WillyCcV19/PI_Equipo_04/ProyectoIntegrador/Entegables/P-CajaFuncionesYEsquemaFunciones.md

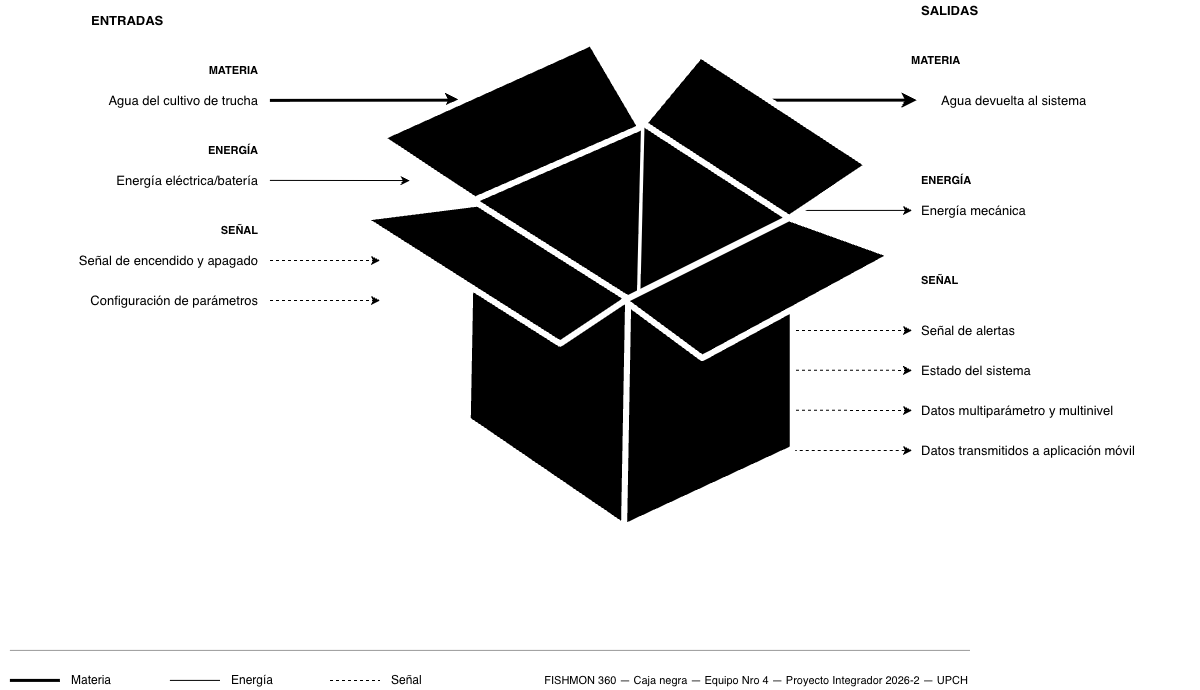
[picture p103: Imagenes/func/cajanegra-final.png]

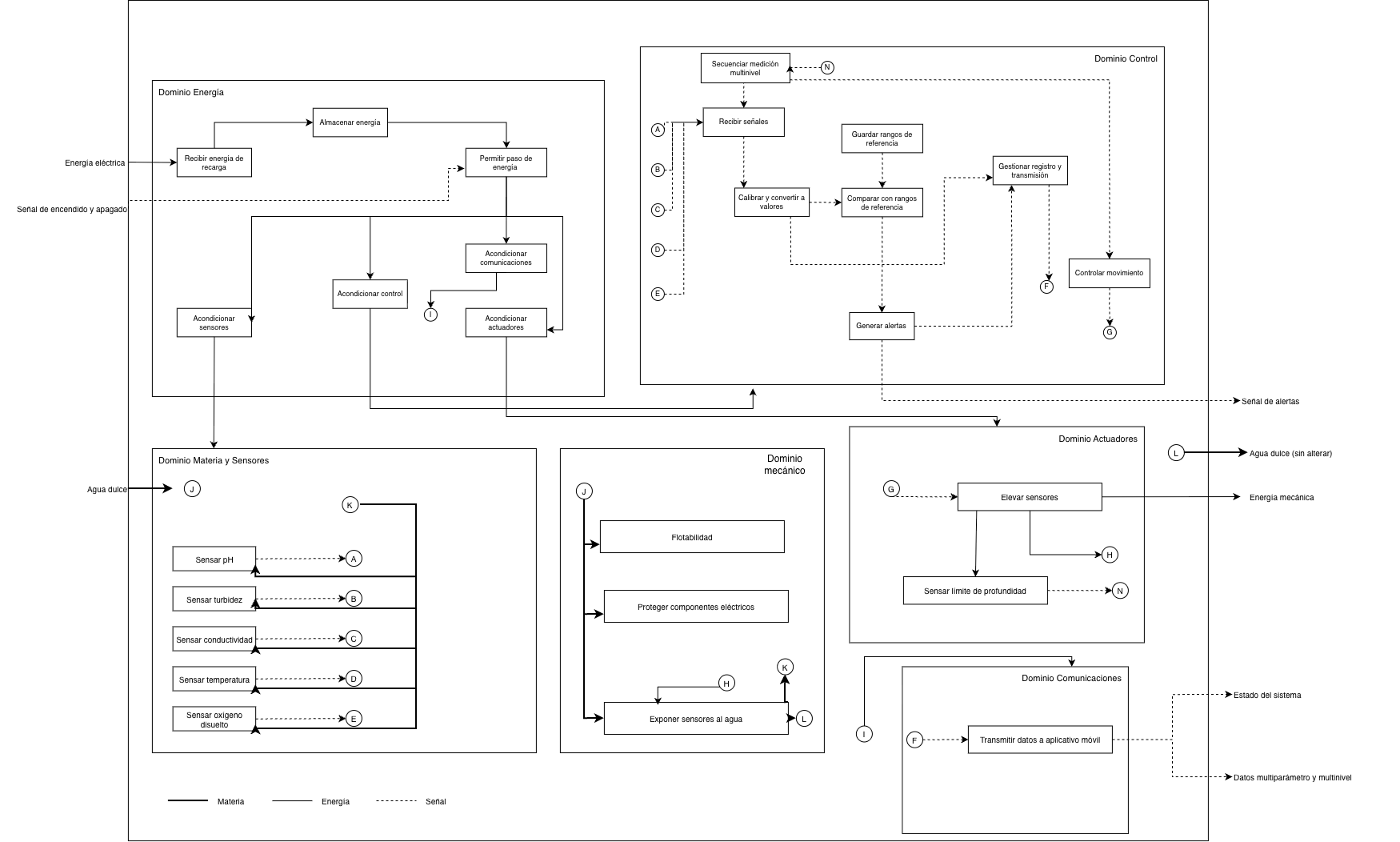
[picture p104: Imagenes/func/esquematico-final.png]
