WillyCcV19/PI_Equipo_04/ProyectoIntegrador/Talleres/Taller_RedesNeuronales/VerenisseQuispitongo/tallerRDVQ.md

# Redes Neuronales

En este taller se trabajaron diferentes conceptos relacionados con redes neuronales. Se utilizaron Redes Neuronales Convolucionales (CNN) para clasificación de imágenes, Keras para construir una red neuronal de clasificación binaria y finalmente se estudió el funcionamiento básico de un Perceptrón.

## 1.- Redes Neuronales Convencionales (CNN)

Las CNN (Convolutional Neural Networks) son redes neuronales especialmente utilizadas para trabajar con imágenes. Su principal característica es que pueden analizar grupos de píxeles cercanos y aprender automáticamente patrones presentes en una imagen.

Para ello utilizan pequeños filtros llamados kernels, los cuales recorren la imagen buscando características como bordes, formas, texturas y estructuras.

En una CNN se pueden identificar principalmente los siguientes componentes:

- **Conv2D:** aplica filtros sobre la imagen para extraer características.
- **ReLU:** transforma los valores negativos en cero y mantiene los valores positivos.
- **MaxPooling:** reduce el tamaño de la información manteniendo las características más importantes.
- **Capas densas:** utilizan las características encontradas para realizar finalmente la clasificación.

Para esta parte del taller se utilizó el dataset **TrashNet**, compuesto por imágenes de diferentes tipos de residuos.

En el ejercicio se trabajó específicamente con imágenes correspondientes a:

> **Glass (vidrio)**  
> **Plastic (plástico)**

Las imágenes fueron transformadas a escala de grises para utilizarlas como entrada del modelo.

<p align="center">
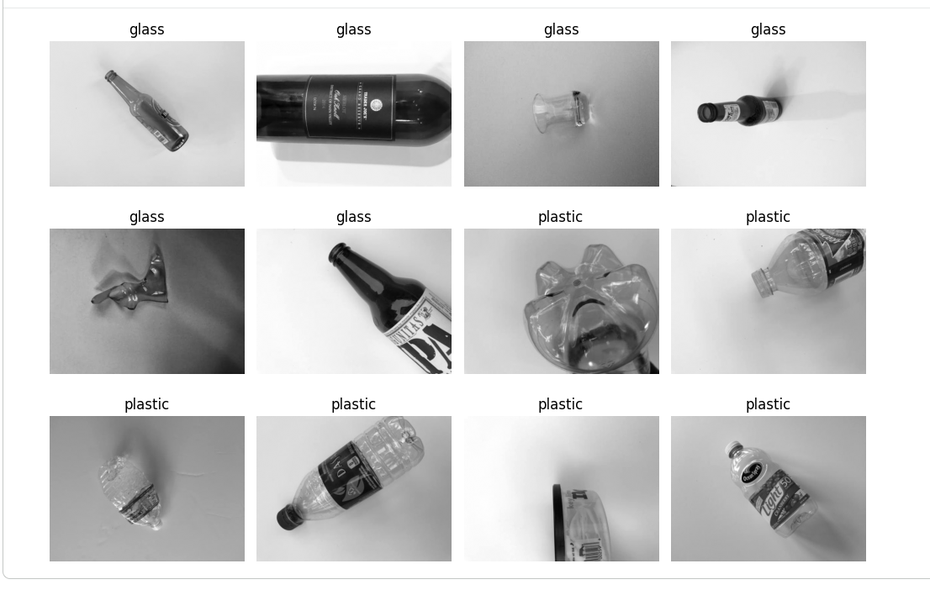
[picture p120: Imagenes/TallerRedesNeuronales/Screenshot 2026-09-22 153117.png]
  
</p>

### Construcción de la CNN

Se creó una CNN desde cero utilizando PyTorch.

El modelo está formado por varias capas convolucionales: A medida que la imagen pasa por las diferentes capas, el modelo va aprendiendo características cada vez más específicas. Las primeras capas pueden detectar características simples, mientras que las capas posteriores combinan esta información para distinguir entre vidrio y plástico.

### Entrenamiento del modelo

La CNN fue entrenada durante varias épocas utilizando los datos de entrenamiento.
<p align="center">
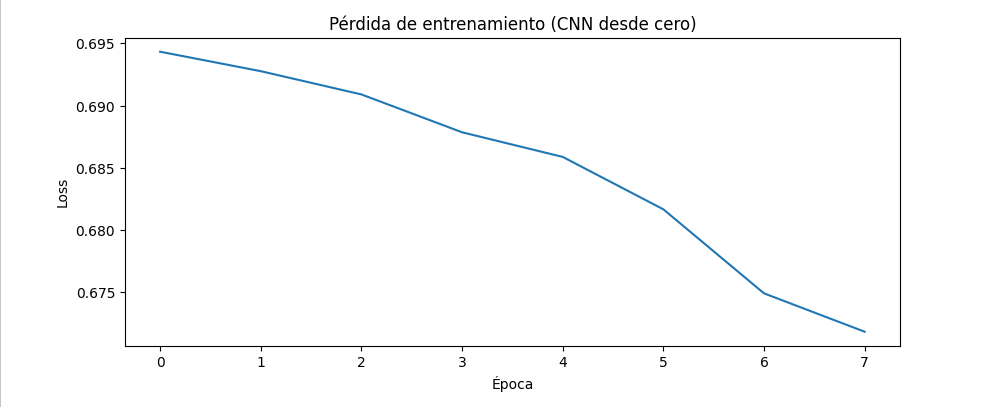
[picture p121: Imagenes/TallerRedesNeuronales/Screenshot 2026-09-22 154243.png]
  
</p>
En la gráfica se observa que la pérdida disminuye progresivamente. Esto indica que el modelo está aprendiendo durante el entrenamiento.
<p align="center">
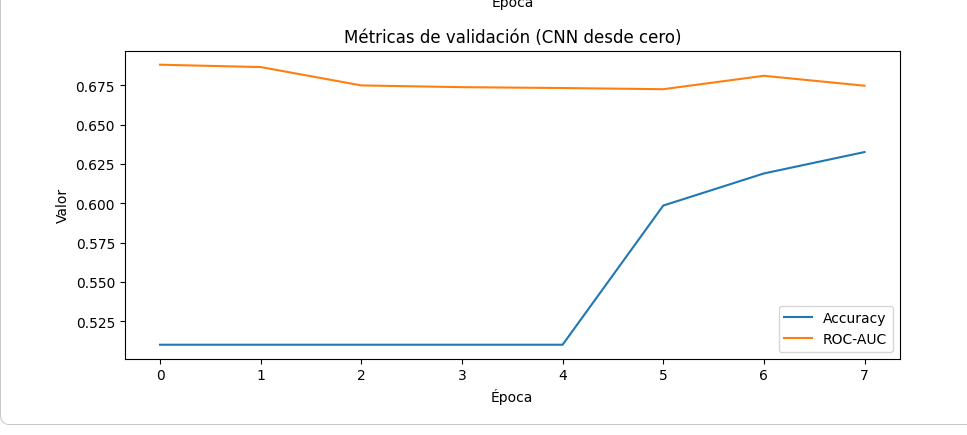
[picture p122: Imagenes/TallerRedesNeuronales/Screenshot 2026-09-22 154420.png]
  
</p>
Durante las primeras épocas la exactitud se mantiene baja, pero posteriormente comienza a mejorar hasta alcanzar aproximadamente un 63.27 % de accuracy en validación.

El ROC-AUC se mantiene aproximadamente entre 0.67 y 0.69, por lo que el modelo logra diferenciar las clases, aunque todavía presenta dificultades.

### Data Augmentation

Posteriormente se utilizó Data Augmentation, realizando pequeñas modificaciones en las imágenes durante el entrenamiento, como rotaciones y desplazamientos.

El objetivo es evitar que el modelo memorice únicamente las imágenes originales y mejorar su capacidad para reconocer nuevos ejemplos.

Los resultados obtenidos fueron:

| Modelo | Accuracy | ROC-AUC |
|---|---:|---:|
| CNN sin augmentation | 55.03 % | 0.6191 |
| CNN con augmentation | 56.38 % | 0.6411 |

Se observa una pequeña mejora al utilizar aumento de datos.

### Transfer Learning

También se aplicó Transfer Learning utilizando una red ResNet18 previamente entrenada.

En este caso no se comienza completamente desde cero, sino que se aprovechan características que la red ya había aprendido anteriormente sobre otras imágenes.

Después del entrenamiento y Fine-Tuning se obtuvo:

> **Accuracy: 86.58 %**  
> **ROC-AUC: 0.9562**

El resultado es considerablemente superior al obtenido con la CNN creada desde cero, mostrando la utilidad del Transfer Learning cuando se dispone de una cantidad limitada de imágenes.

### Interpretabilidad mediante Grad-CAM

Finalmente se utilizó Grad-CAM para visualizar qué regiones de una imagen fueron más importantes para que la red realizara una predicción.
<p align="center">
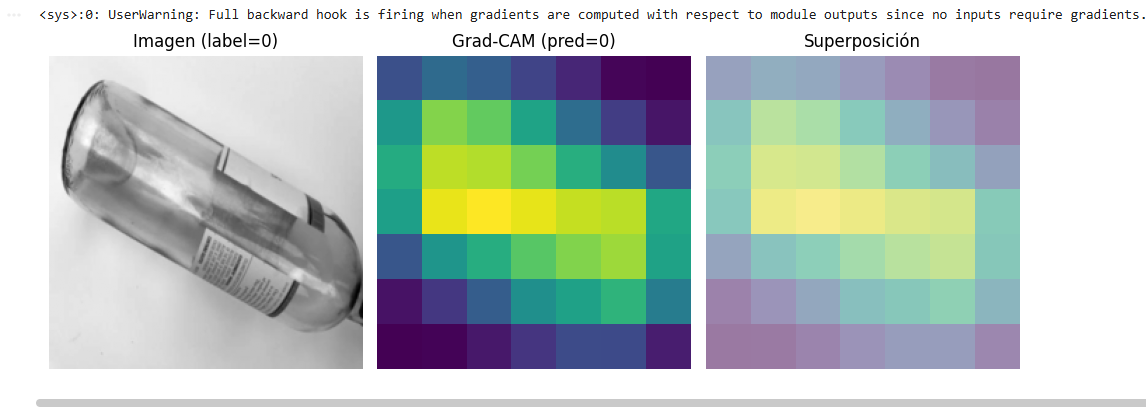
[picture p123: Imagenes/TallerRedesNeuronales/Screenshot 2026-09-22 154939.png]
  
</p>

Las regiones más claras o amarillas representan las zonas que tuvieron mayor influencia en la decisión del modelo.
Las regiones más oscuras representan zonas que tuvieron una menor participación en la predicción.
Esto permite tener una idea de qué partes de la imagen está utilizando la CNN para distinguir entre los diferentes residuos.

# 2. Clasificación binaria utilizando Keras

En la segunda parte se utilizó Keras, una librería que facilita la creación y entrenamiento de redes neuronales.

En este ejercicio se trabajó con el dataset IMDB, que contiene reseñas de películas. El objetivo fue clasificar cada reseña en una de dos categorías:
> **0 → Reseña negativa**  
> **1 → Reseña positiva**

## Preparación de los datos

Las palabras de las reseñas se encuentran inicialmente representadas mediante números. Posteriormente se realizó una transformación de los datos mediante una representación tipo One-Hot Encoding**, generando vectores de 10 000 posiciones.De esta manera, la red neuronal puede trabajar con la información de las reseñas en forma numérica.

## Construcción del modelo

La red fue construida utilizando `Sequential` de Keras. El modelo posee dos capas ocultas de **16 neuronas** y una capa final con una sola neurona. La función `ReLU` se utiliza en las capas internas, mientras que `sigmoid` se utiliza en la salida porque el problema tiene únicamente dos posibles resultados. La salida de `sigmoid` puede interpretarse como una probabilidad entre 0 y 1.

## Entrenamiento y sobreajuste

El modelo fue entrenado durante 20 épocas.



En la gráfica se observa que el error de entrenamiento disminuye a medida que avanzan las épocas. Sin embargo, aproximadamente desde la época 4 o 5, el error de validación comienza a aumentar. Este comportamiento indica un caso de **sobreajuste**, ya que el modelo continúa aprendiendo los datos de entrenamiento, pero comienza a perder capacidad para generalizar correctamente a otros datos.

## Comparación con una red más pequeña

También se creó un modelo más pequeño utilizando únicamente cuatro neuronas en la capa oculta.

El modelo pequeño mantiene durante más épocas un valor de pérdida de validación relativamente estable.
Esto permite observar que reducir la complejidad de una red puede ayudar a disminuir el sobreajuste.

## Regularización

Posteriormente se aplicó regularización **L2**. La regularización penaliza los pesos demasiado grandes y busca que el modelo aprenda una solución menos dependiente de los datos de entrenamiento. Esto puede producir inicialmente un error mayor, pero busca mejorar la capacidad de generalización.

## Dropout

También se utilizó **Dropout**. Durante el entrenamiento se desactiva aleatoriamente aproximadamente el 50 % de las neuronasde esa capa.bEsto obliga a la red a no depender siempre de las mismas neuronas y permite reducir el riesgo de sobreajuste.

## Predicción

Finalmente se realizaron predicciones utilizando:

```python
predictions = model.predict(x_test)
```

Por ejemplo, para uno de los elementos del conjunto de prueba se obtuvo:

```python
array([0.99375147])
```

Este valor equivale aproximadamente a una probabilidad de:

> **99.4 %**

Por lo tanto, el modelo interpreta esa reseña como **positiva** con una probabilidad elevada.

# 3. Perceptrón

El funcionamiento del Perceptrón consiste en recibir diferentes entradas, asignar un peso a cada una, sumar los resultados y finalmente utilizar una función de activación para obtener una salida.
De manera general puede representarse como:

> **Salida = función de activación (entradas × pesos + bias)**

En el taller se utilizó el siguiente ejemplo:

temperatura = 100
vibracion = 50
weights = np.array([0.5, -0.5])
bias = -30

Las variables utilizadas fueron la temperatura y vibración de un equipo industrial.
La suma ponderada obtenida es:

(100 × 0.5) + (50 × -0.5) - 30
50 - 25 - 30 = -5

Como el resultado es negativo, la función escalón devuelve: 0
Por lo tanto, el resultado obtenido fue:
> **El equipo no presenta una alerta de sobrecalentamiento.**

También se utilizó la función `tanh`, obteniendo aproximadamente:
-0.9999

Al ser un valor negativo, la interpretación también corresponde a la ausencia de una alerta.

## Perceptrón como compuerta AND

Se probaron diferentes pesos para observar cómo un perceptrón puede representar operaciones lógicas.
Con:
```python
weights = np.array([0.4, 0.4])
bias = -0.5
```
El resultado corresponde a una compuerta **AND**, ya que solamente produce `1` cuando ambas entradas tienen el valor `1`.

## Perceptrón como compuerta OR

Para representar OR se utilizaron:
```python
weights = np.array([2, 1])
bias = -0.5
```
En este caso el perceptrón genera una salida `1` cuando al menos una de las entradas tiene el valor `1`.

## Limitación del perceptrón: XOR

La compuerta XOR presenta el siguiente comportamiento:



En este gráfico los casos que pertenecen a la misma clase no pueden separarse utilizando una única línea recta.
Por esta razón:
**Un solo perceptrón no puede resolver XOR.**
Para resolver este problema se necesitan varias neuronas trabajando juntas, por ejemplo:
**2 perceptrones + una capa de salida**
Este ejemplo permite entender por qué las redes neuronales utilizan varias neuronas y varias capas: existen problemas que una única neurona no puede representar por sí sola.

# 4.- ¿Cuál Red Neuronal usarian en su proyecto?

Para el proyecto **Fishmoon** se propone utilizar una red neuronal multicapa implementada con **Keras** para estimar el nivel de oxígeno disuelto en el agua.
La elección se debe a que Fishmoon trabajaría principalmente con datos numéricos obtenidos de sensores, como:

- Temperatura
- pH
- Turbidez
- Conductividad

A partir de estas variables, el modelo tendría como objetivo estimar un valor numérico de oxígeno disuelto expresado en **mg/L**.

### ¿Por qué no utilizar una CNN?

Las redes neuronales convolucionales (CNN) son especialmente útiles cuando se trabaja con imágenes, ya que pueden reconocer patrones espaciales como bordes, formas y texturas. En Fishmoon, las entradas principales serían valores numéricos provenientes de sensores y no imágenes. Por esta razón, una CNN no sería necesaria para esta función.

### ¿Por qué no utilizar un perceptrón simple?

Un perceptrón simple puede realizar decisiones básicas, por ejemplo:

**0 → condición normal**  
**1 → condición de alerta**

Sin embargo, presenta limitaciones cuando existen relaciones más complejas entre varias variables. En Fishmoon no se busca únicamente indicar si existe o no una alerta, sino estimar un valor continuo, por ejemplo:

**Oxígeno disuelto estimado = 6.4 mg/L**

Además, variables como la temperatura, el pH, la turbidez y la conductividad pueden relacionarse de diferentes maneras con el oxígeno disuelto, por lo que una sola neurona podría resultar insuficiente.

### ¿Por qué una MLP con Keras?

Una red neuronal multicapa (MLP) permite utilizar varias variables de entrada y varias capas de neuronas para aprender relaciones más complejas entre los datos.

Su estructura podría ser:

Temperatura -------pH --------Turbidez ----------Conductividad ---------> Red neuronal MLP implementada con Keras --------> Oxígeno disuelto estimado: 6.4 mg/L
