WillyCcV19/PI_Equipo_04/Imagenes/func/BOCETO_2.0.png

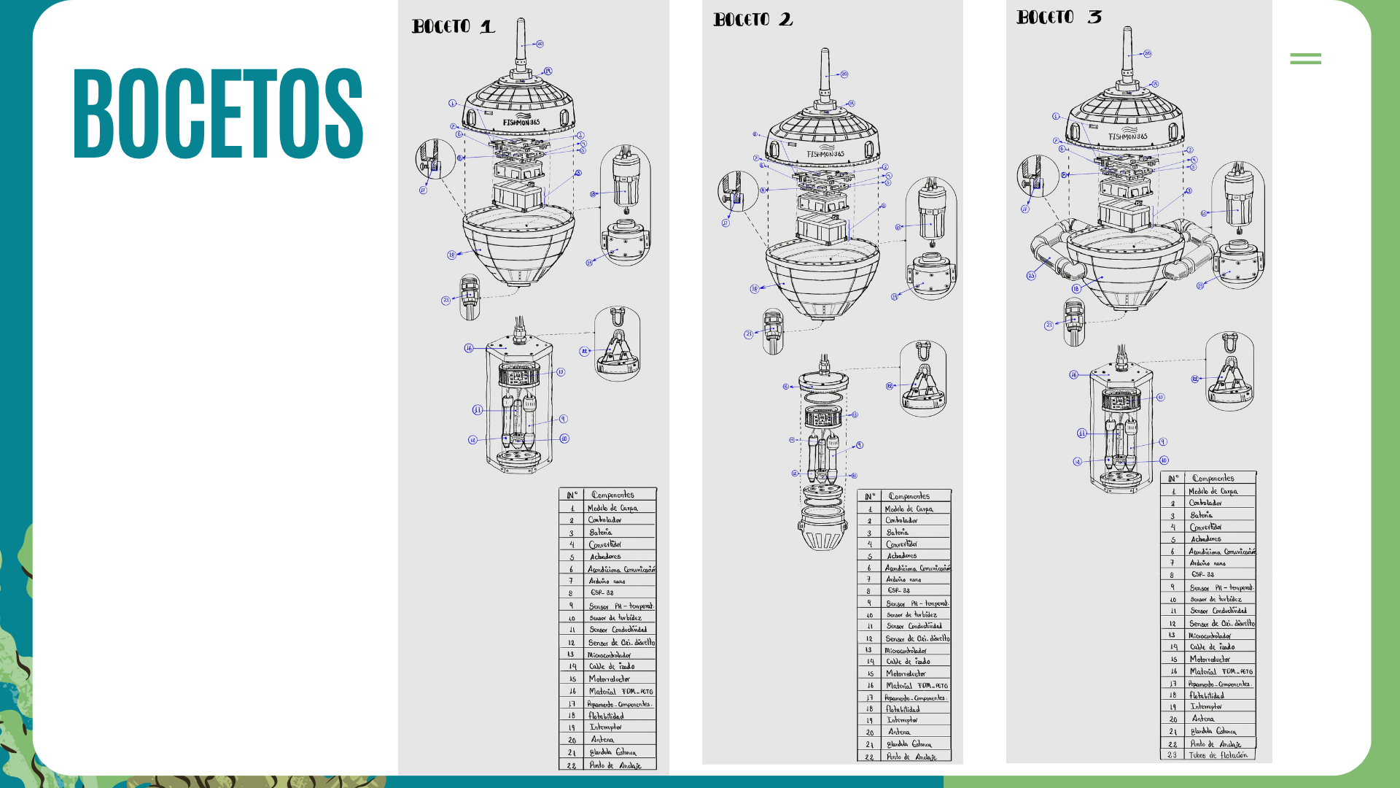
Imagenes/func/BOCETO_2.0.png
