WillyCcV19/PI_Equipo_04/Imagenes/func/comparacion_matriz_morfologica_new.png

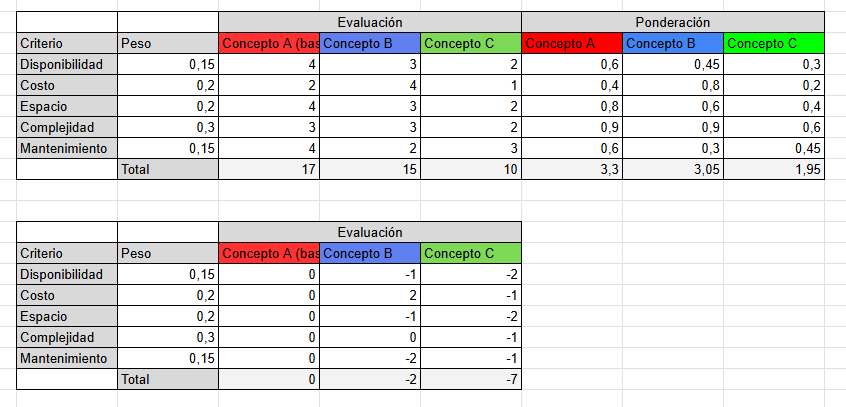
Imagenes/func/comparacion_matriz_morfologica_new.png
