WillyCcV19/PI_Equipo_04/Imagenes/func/MATRIZ MORFOLÓGICA.png

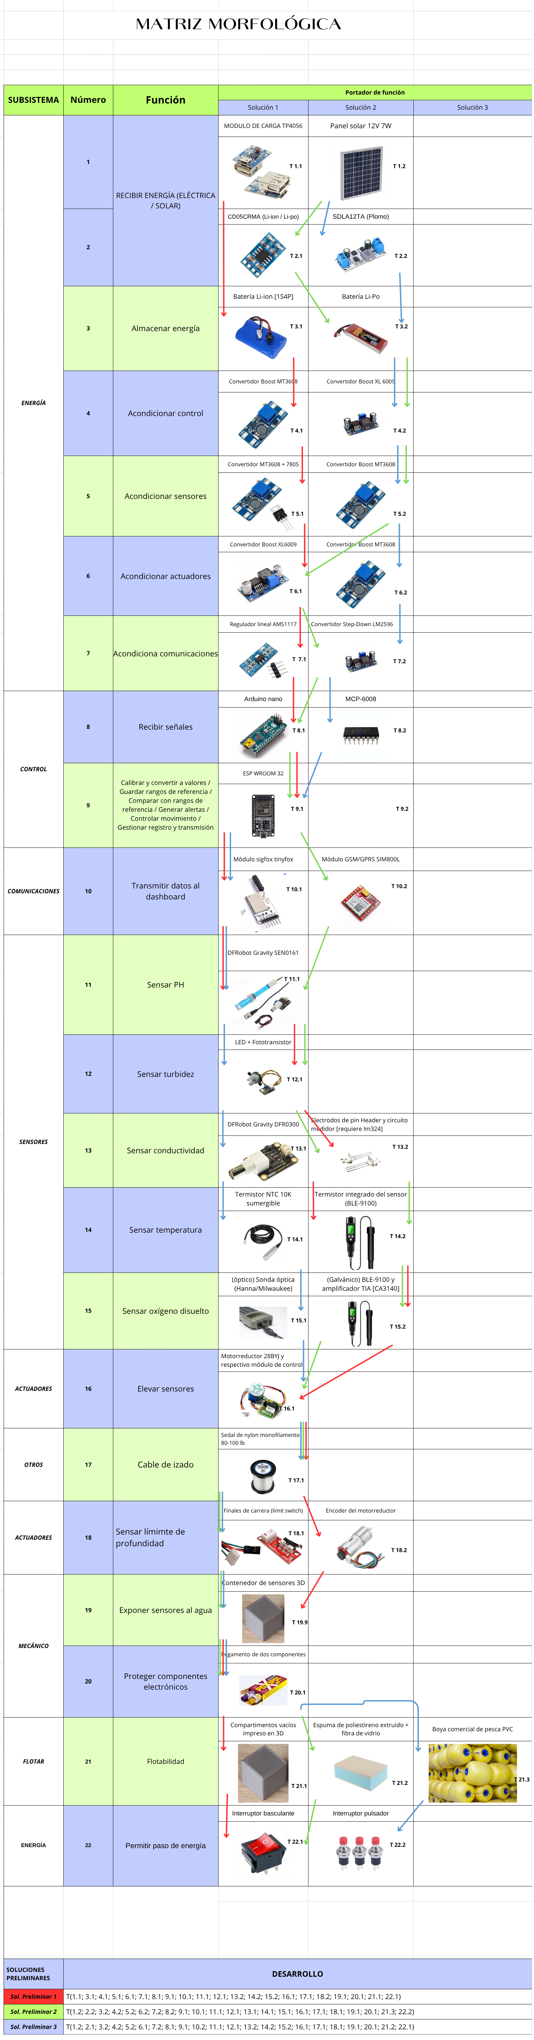
Imagenes/func/MATRIZ MORFOLÓGICA.png
