WillyCcV19/PI_Equipo_04/Imagenes/Integrantes/referencia.jpeg

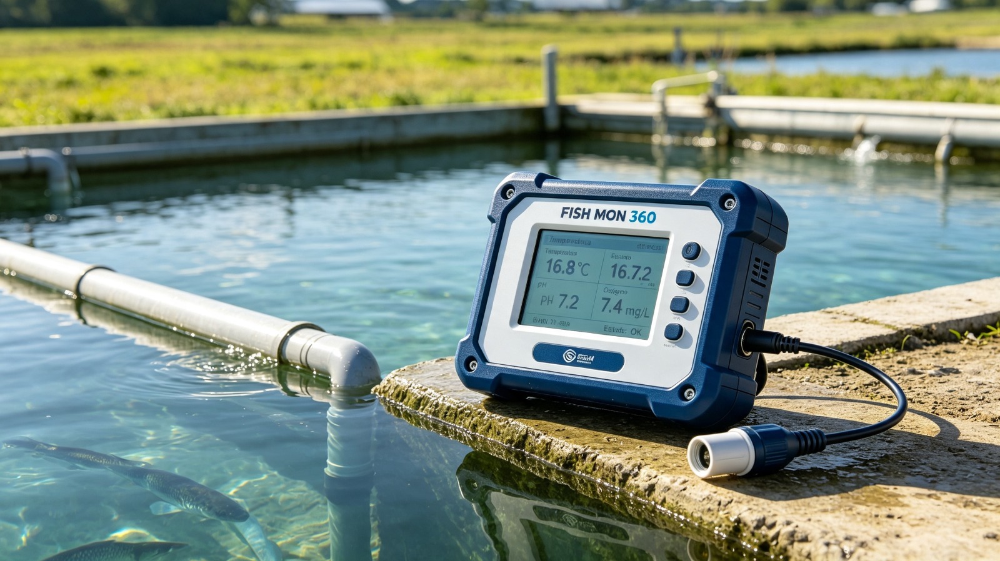
Imagenes/Integrantes/referencia.jpeg
