WillyCcV19/PI_Equipo_04/Imagenes/ModuloElec/reporte_preliminar/img1.jpeg

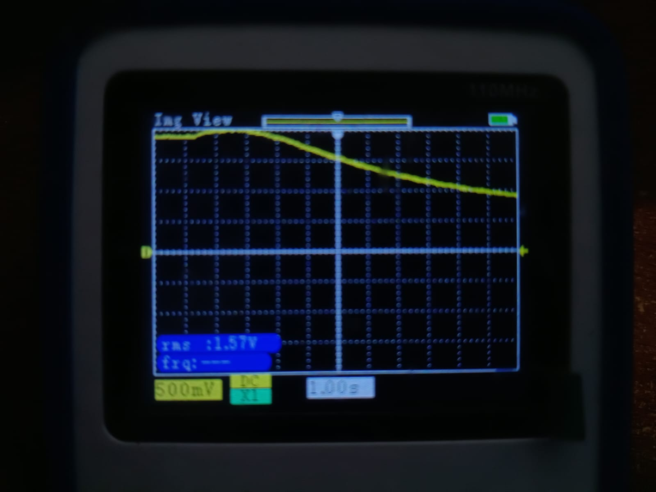
Imagenes/ModuloElec/reporte_preliminar/img1.jpeg
