WillyCcV19/PI_Equipo_04/Imagenes/Simulaciones/Engranaje3.png

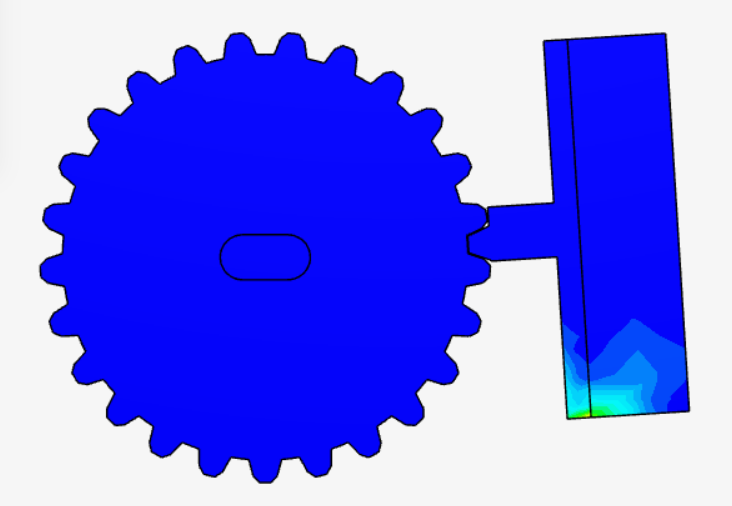
Imagenes/Simulaciones/Engranaje3.png
