WillyCcV19/PI_Equipo_04/Imagenes/Simulaciones/Engranaje4.png

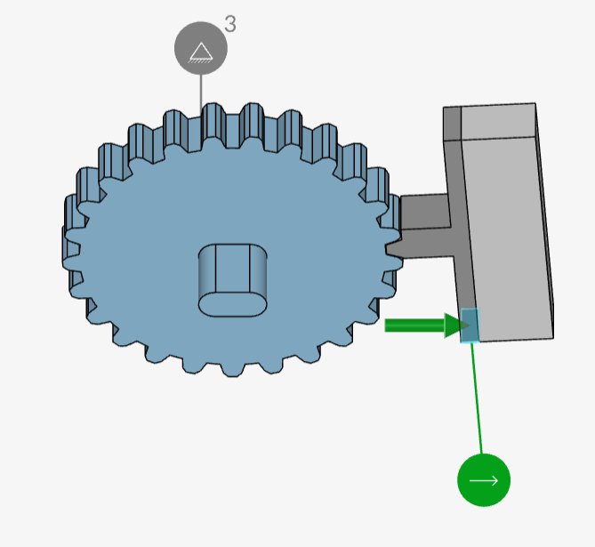
Imagenes/Simulaciones/Engranaje4.png
