WillyCcV19/PI_Equipo_04/Imagenes/Simulaciones/Screenshot 2026-08-27 164050.png

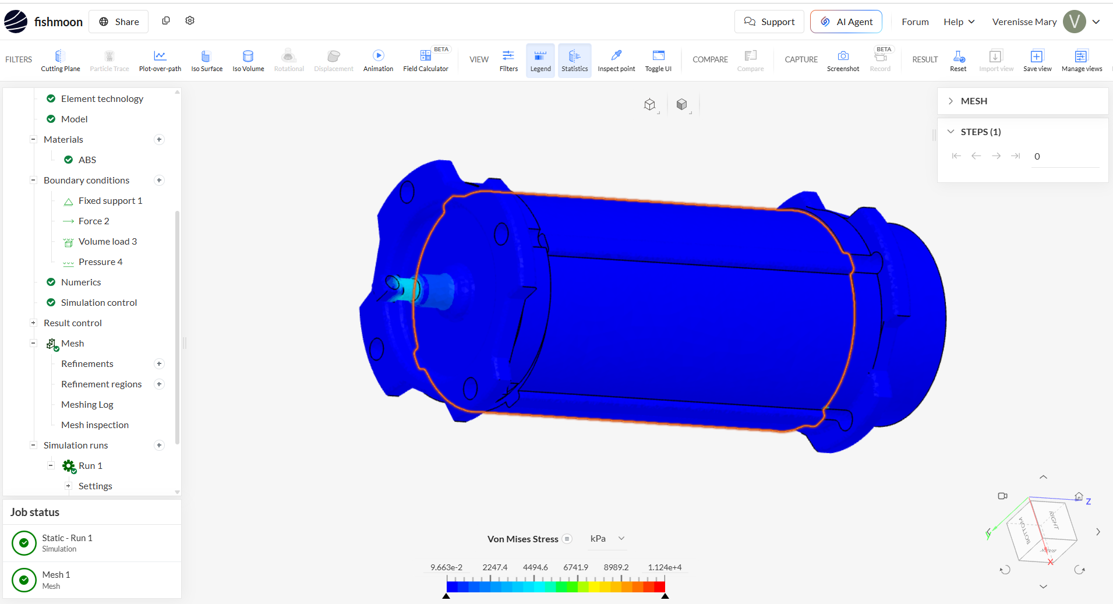
Imagenes/Simulaciones/Screenshot 2026-08-27 164050.png
