WillyCcV19/PI_Equipo_04/Imagenes/TallerIA/Semana5_Tarea/eber/123.png

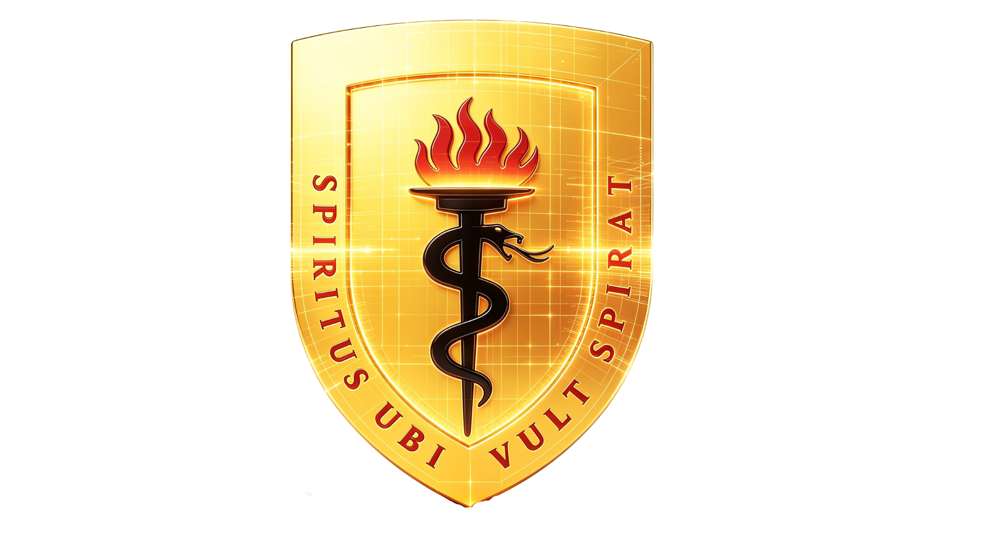
Imagenes/TallerIA/Semana5_Tarea/eber/123.png
