WillyCcV19/PI_Equipo_04/ProyectoIntegrador/Talleres/Taller_EasyEDA/Ruben Cabrera/Captura de pantalla 2026-09-10 a la(s) 2.56.32 p. m..png

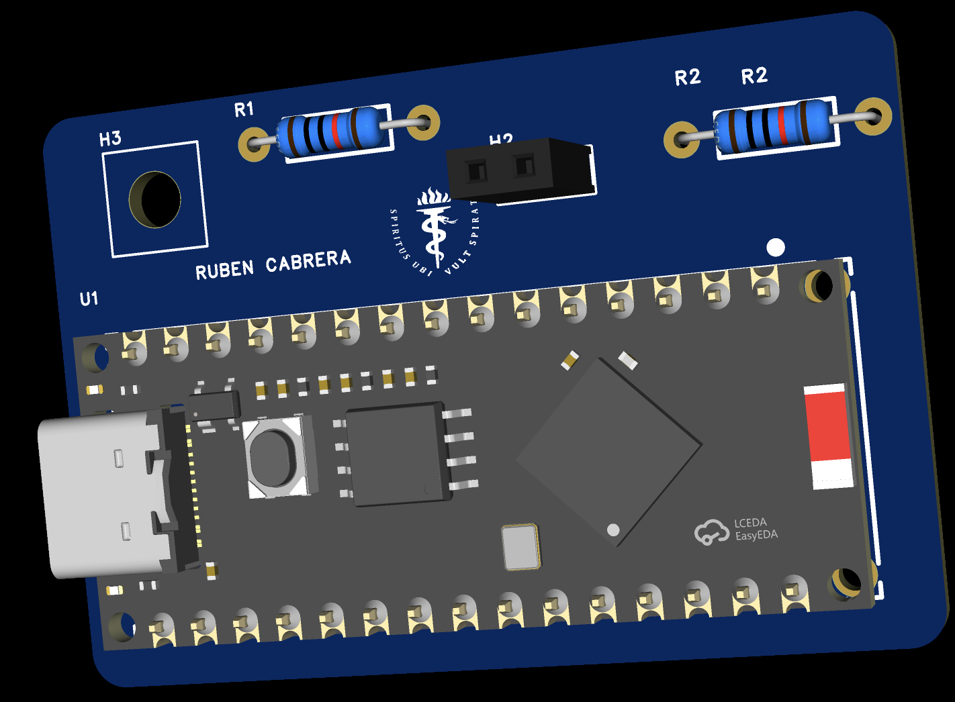
ProyectoIntegrador/Talleres/Taller_EasyEDA/Ruben Cabrera/Captura de pantalla 2026-09-10 a la(s) 2.56.32 p. m..png
