WillyCcV19/PI_Equipo_04/ProyectoIntegrador/Talleres/Taller_EasyEDA/Willy Ccatamayo/CapturaTaller.png

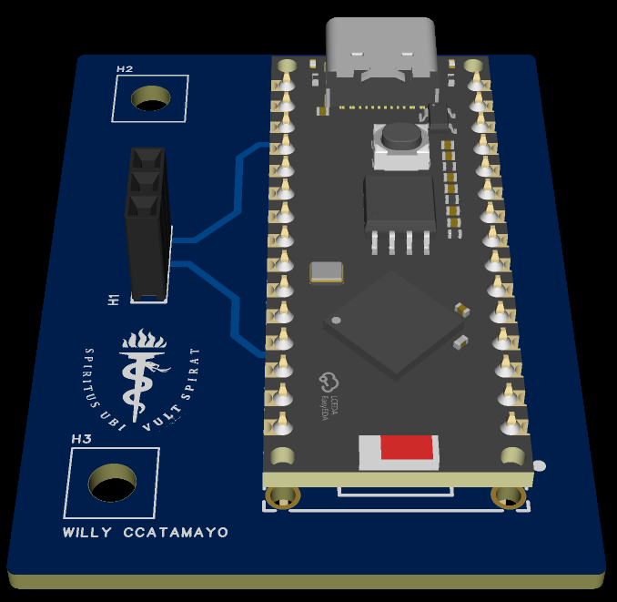
ProyectoIntegrador/Talleres/Taller_EasyEDA/Willy Ccatamayo/CapturaTaller.png
